wpwrak/antorcha/hw/accel.sch

## KiCad design hw/accel.sch (2012-06-16)

Schematic: accel.sch

Parts:
C801, C802, C803: 100n
U801: ADXL32X
