wpwrak/antorcha/hw/battery.sch

## KiCad design hw/battery.sch (2012-06-12)

Schematic: battery.sch

Parts:
CON501, CON502, CON503, CON504, CON505: CONN_4
