wpwrak/antorcha/hw/control.sch

## KiCad design hw/control.sch (2012-06-16)

Schematic: control.sch

Parts:
C401, C402: 100n
C403: 1u
CON401: CONN_4
CON402: CONN_18
I401: ATMEGA8
R401: 0R
R406, R407, R408, R409: 10k
TP401, TP402, TP403, TP404, TP405, TP406: TESTPOINT
