wpwrak/antorcha/hw/leda.sch

## KiCad design hw/leda.sch (2012-06-16)

Schematic: leda.sch

Parts:
CON201: CONN_10
D201, D202, D203, D204, D205, D206, D207, D208, D209, D210, D211, D212, D213, D214, D215, D216: LED
Q201, Q202, Q203, Q204, Q205, Q206, Q207, Q208: NPN-SOT-BEC
R201, R202, R205, R206, R209, R210, R213, R214: 56
R203, R204, R207, R208, R211, R212, R215, R216: 4k7
