wpwrak/antorcha/hw/ledb.sch

## KiCad design hw/ledb.sch (2012-06-12)

Schematic: ledb.sch

Parts:
CON301: CONN_10
CON302: CONN_18
D301, D302, D303, D304, D305, D306, D307, D308, D309, D310, D311, D312, D313, D314, D315, D316: LED
Q301, Q302, Q303, Q304, Q305, Q306, Q307, Q308: NPN-SOT-BEC
R301, R302, R305, R306, R309, R310, R313, R314: 56
R303, R304, R307, R308, R311, R312, R315, R316: 4k7
