wpwrak/antorcha/hw/rf.sch

## KiCad design hw/rf.sch (2012-06-16)

Schematic: rf.sch

Parts:
ANT701: 50R
B701: BALUN-SMT6
C601, C604: 12p
C602, C603, C608, C609: 1u
C605, C606, C607: 22pF/RF
R601: 10k
R602, R603, R604, R605: 22k
TP601: TESTPOINT
U701: AT86RF231
X701: XTAL-4
