wpwrak/antorcha/whirl/whirl.sch

## KiCad design whirl/whirl.sch (2012-11-04, an earlier design)

Schematic: whirl.sch

Parts:
C1, C2: C
CON1, CON2: CONN_6
D1, D2, D3, D4, D5, D6, D7, D8, D9, D10, D11, D12, D13, D14, D15, D16: LED
Q1, Q2, Q3, Q4, Q5, Q6, Q7, Q8, Q9, Q10, Q11, Q12, Q13, Q14, Q15, Q16: NMOSFET-GSD
R1, R2, R3, R4, R5, R6, R7, R8, R9, R10, R11, R12, R13, R14, R15, R16: R
U1, U2: 74X595
