wpwrak/antorcha/tornado/cpu/cpu.sch

## KiCad design tornado/cpu/cpu.sch (2012-12-28, an earlier design)

Schematic: cpu.sch

Parts:
C1: 10u/16V
C2: 22u/6.3V
C3, C4: 100n
CON1, CON2: CONN_1
CON3: CONN_6
CON4: CONN_8
D1: ORANGE
L1: 2.2uH/1.5A
R1: 100
SW1: EVQQ7
U1: TPS6216X
U2: LPC1112FHN33/202
