wpwrak/antorcha/tornado/cpu/per.sch

## KiCad design tornado/cpu/per.sch (2012-12-27)

Schematic: per.sch

Parts:
C5: 10u
C6: 100n
C7: 1u
CON5: MEMCARD8-SHIELD4-SW
Q1: PMOSFET-GSD
U3: LIS3DH
