wpwrak/antorcha/tornado/led/led.sch

## KiCad design tornado/led/led.sch (2012-12-27)

Schematic: led.sch

Parts:
C1: 10u/16V
C2: 22u/6.3V
C3, C4: 100n
CON1, CON2: CONN_8
L1: 2.2uH/1.5A
U1: TPS6216X
U2, U3: 74HC595

Notes on the sheet:
CON1, CON2 are 2 mm PCB contacts
with 50 mil spacing
